YueChengPeng/MagDock/models/pab_fake.pdf

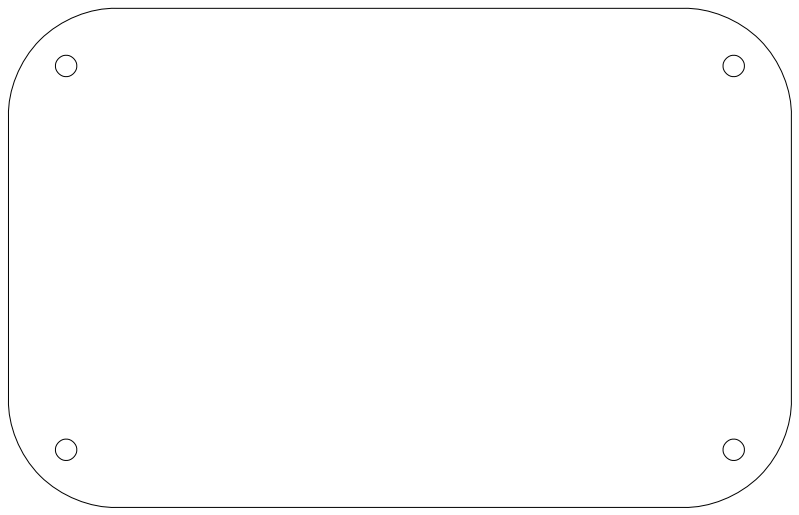
[picture p12: figure]
