YueChengPeng/MagDock/models/slider_acrylic_bottom.pdf

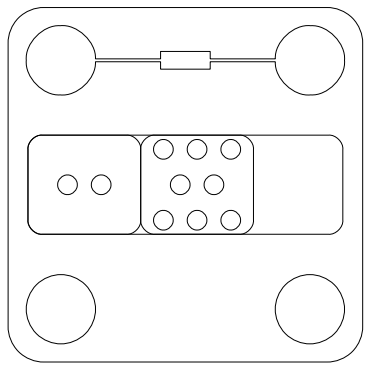
[picture p13: figure]
