YueChengPeng/MagDock/models/top_acrylic.pdf

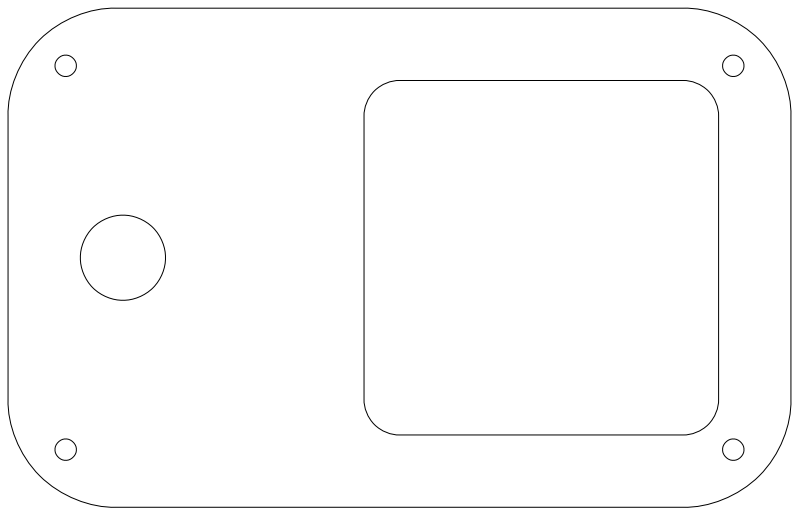
[picture p14: figure]
