YueChengPeng/MagDock/models/slider_firstlayer.pdf

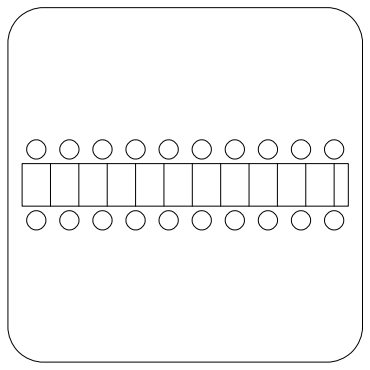
[picture p15: figure]
