YueChengPeng/MagDock/power/Display Device.png

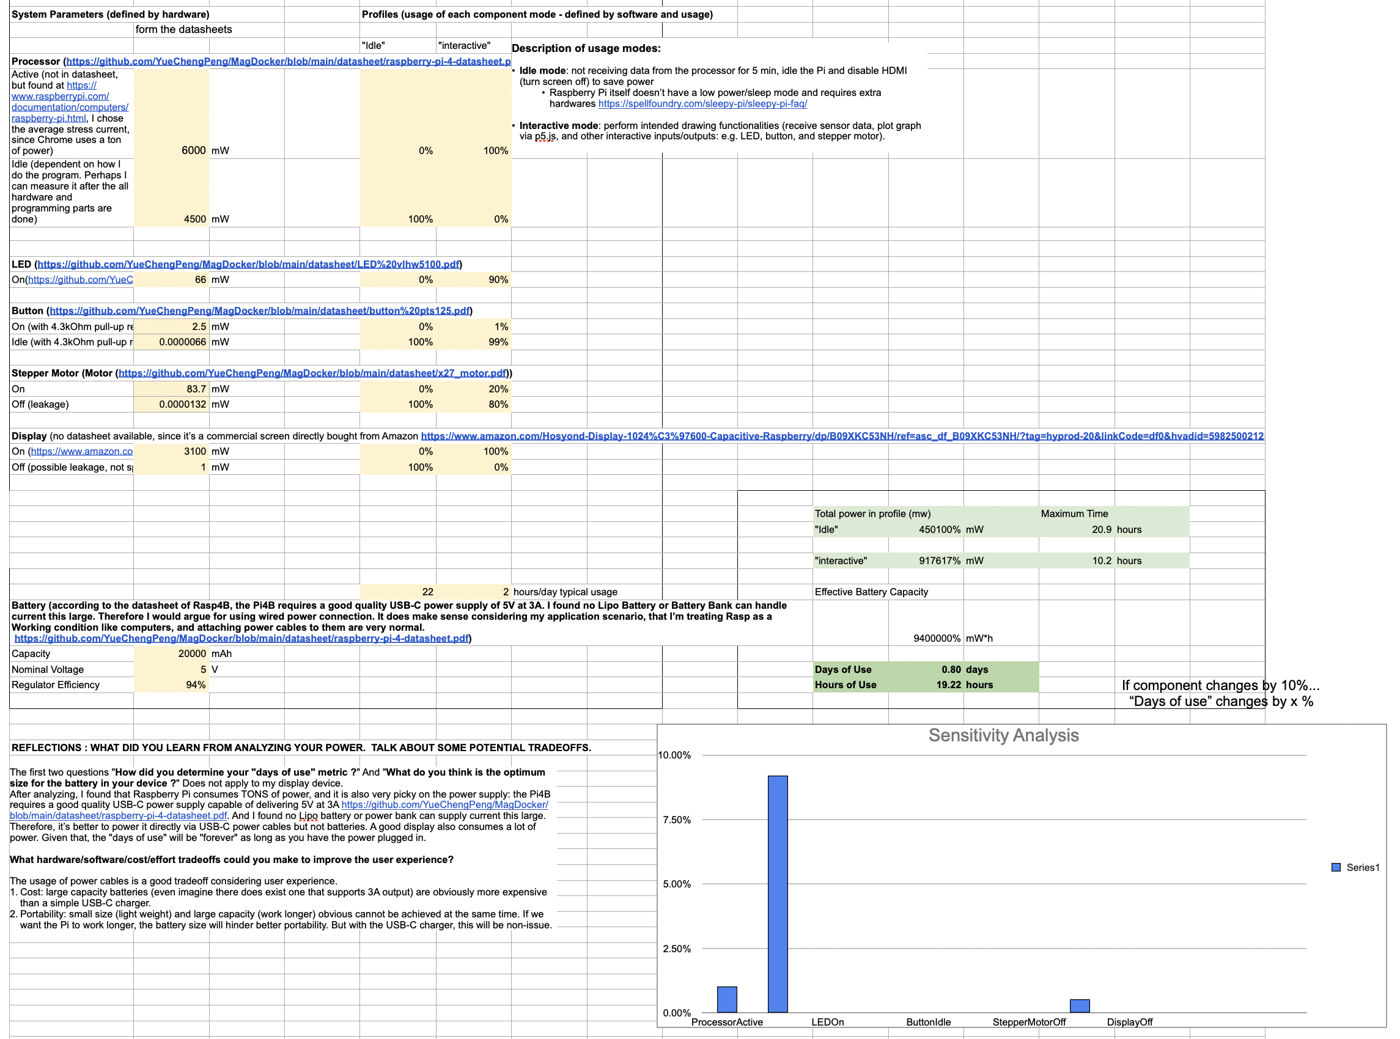
power/Display Device.png
