YueChengPeng/MagDock/power/Sensing Device.png

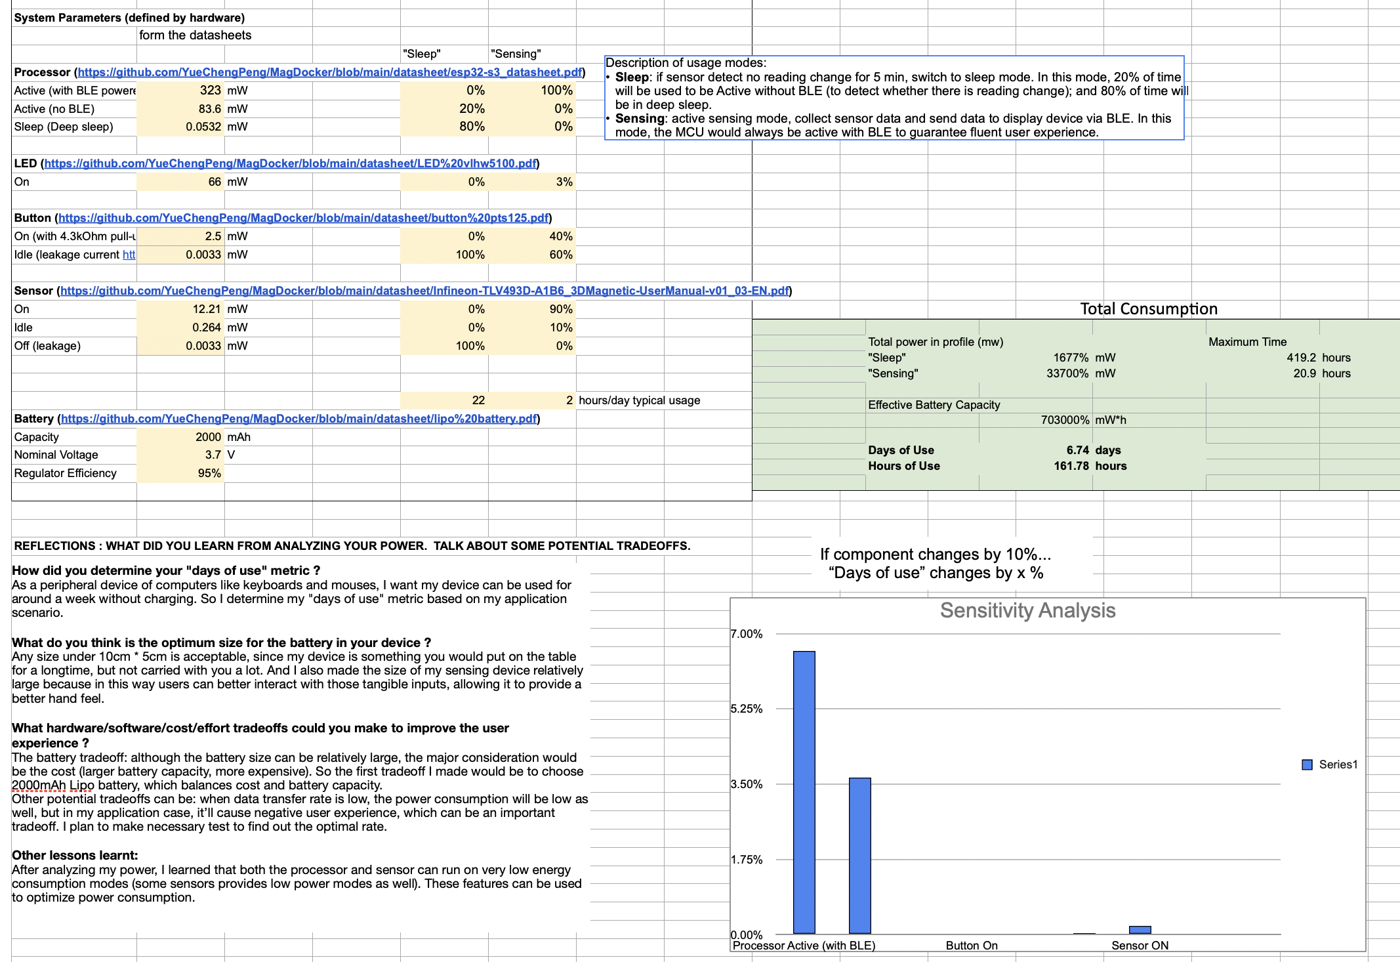
power/Sensing Device.png
