YueChengPeng/MagDock/models/rotary_acrylic.pdf

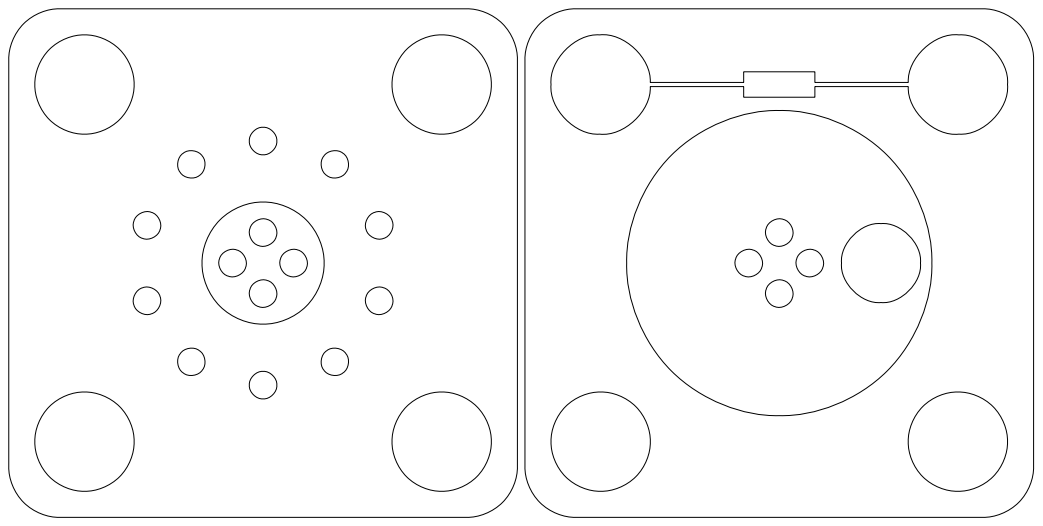
[picture p24: page 1]
