YueChengPeng/MagDock/models/slider_acrylic_top.pdf

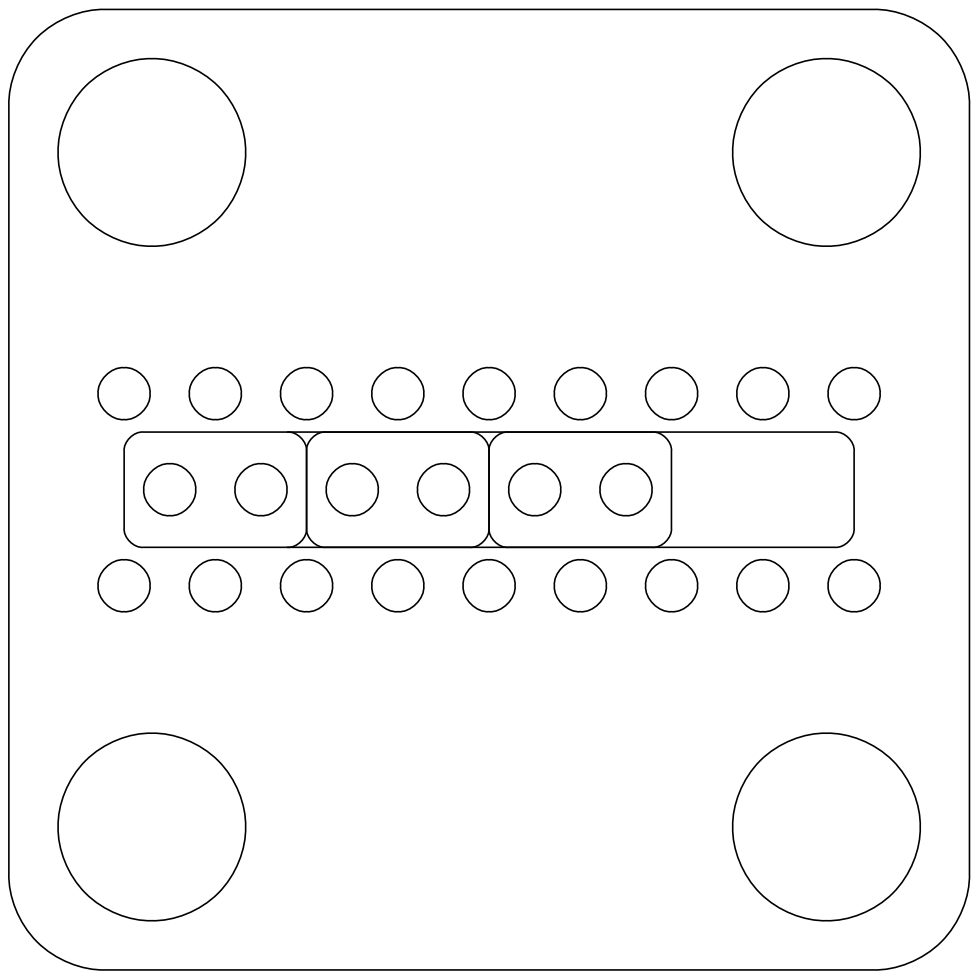
[picture p25: page 1]
