YueChengPeng/MagDock/models/switch_acrylic.pdf

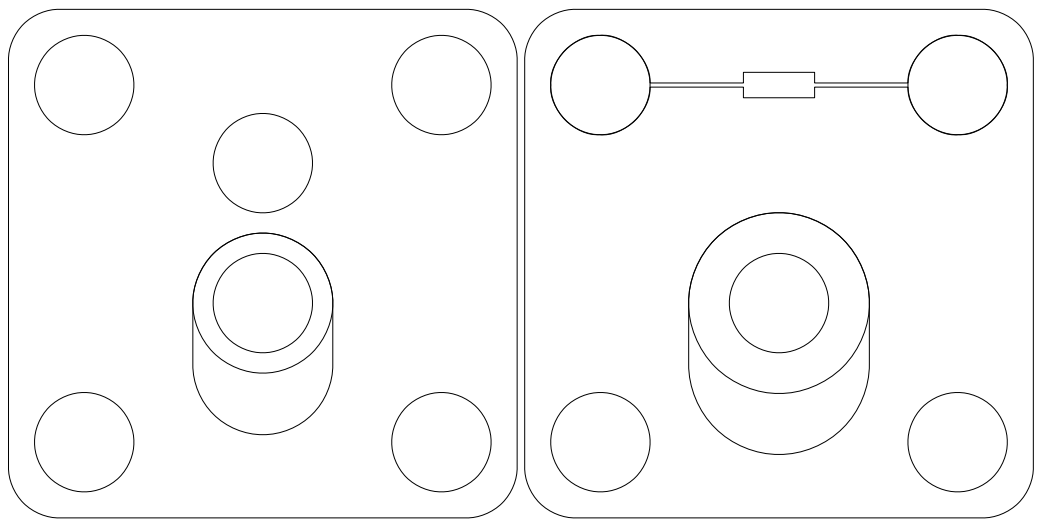
[picture p26: page 1]
