YueChengPeng/MagDock/models/rotary.pdf

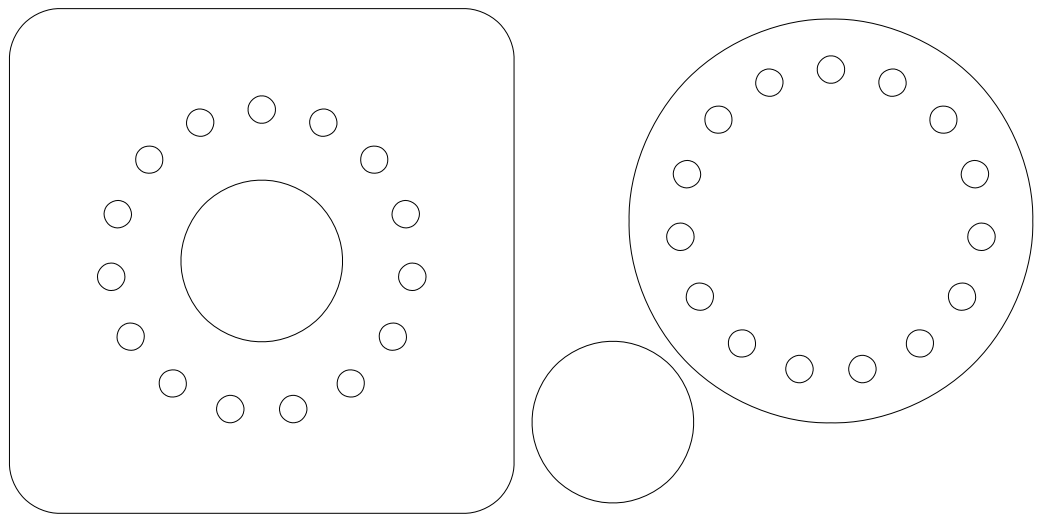
[picture p27: page 1]
